rhiancb30-pixel/Esteira-Seletora/Imagens do Projeto/20251215_132234.jpg

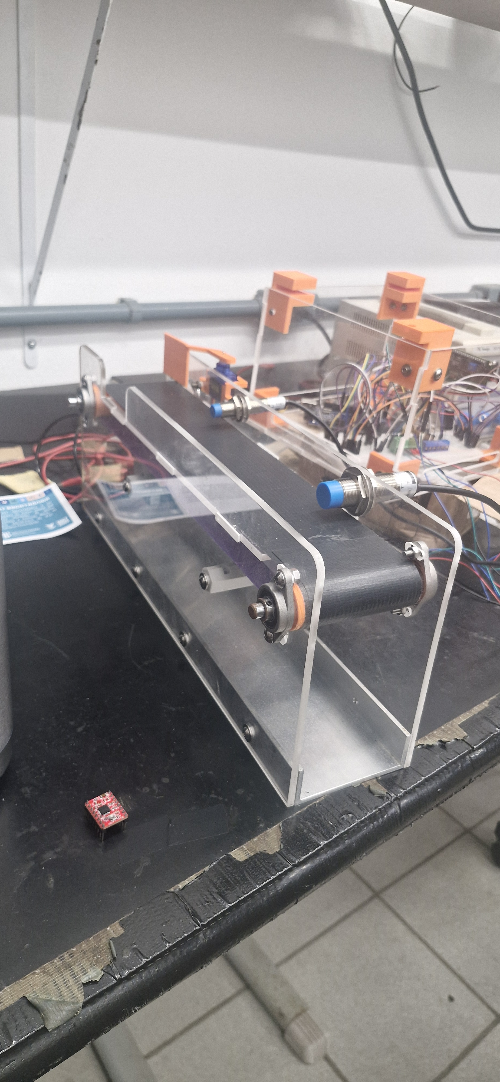
Imagens do Projeto/20251215_132234.jpg
