rhiancb30-pixel/Esteira-Seletora/Imagens do Projeto/20251215_132237.jpg

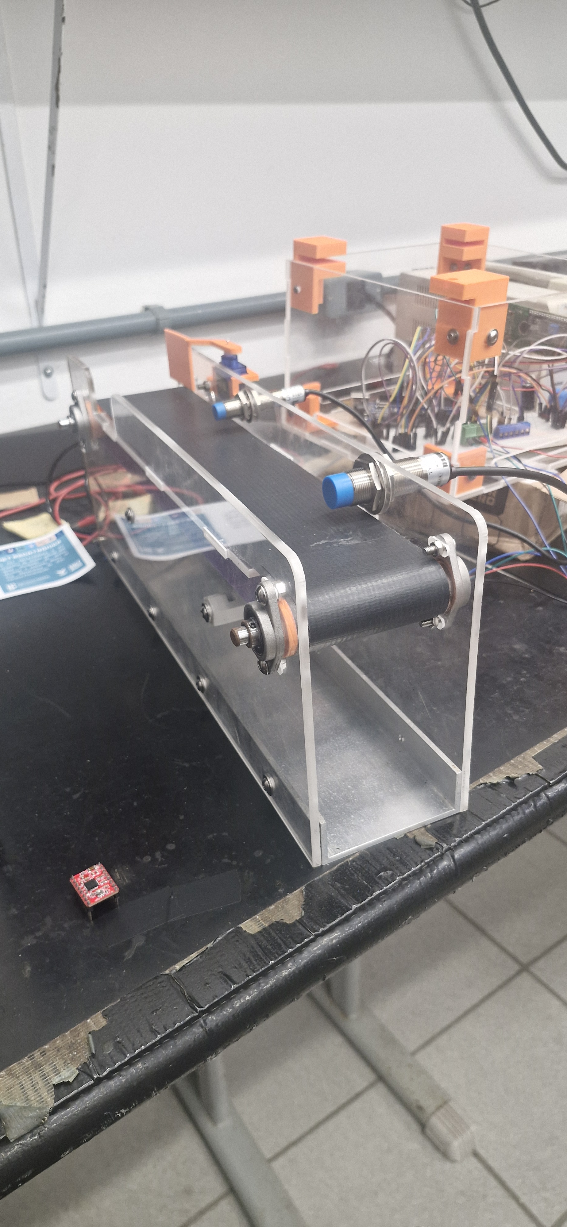
Imagens do Projeto/20251215_132237.jpg
