rhiancb30-pixel/Esteira-Seletora/Caixa/cantoneira_4.SLDPRT

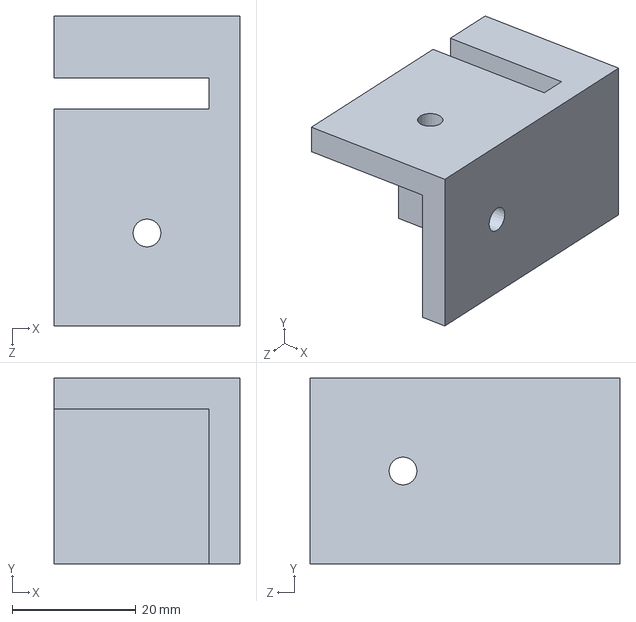
[picture p20: CAD file, 2025-12-16]
Caixa/cantoneira_4.SLDPRT
30.0 x 30.0 x 50.0 mm
