rhiancb30-pixel/Esteira-Seletora/Esteira/Rolete.SLDPRT

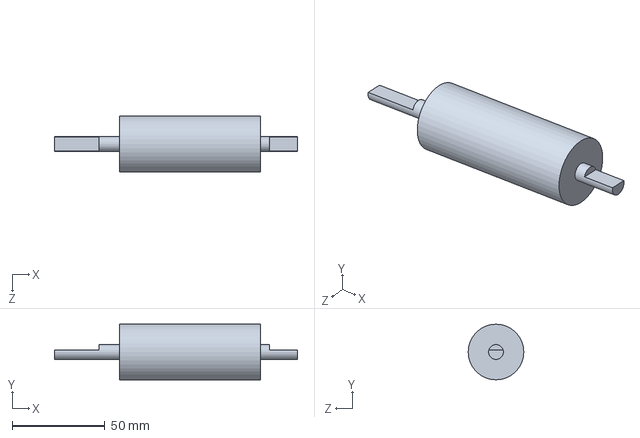
[picture p21: CAD file, 2025-12-16]
Esteira/Rolete.SLDPRT
131.0 x 30.0 x 30.0 mm
