rhiancb30-pixel/Esteira-Seletora/Caixa/Base.SLDPRT

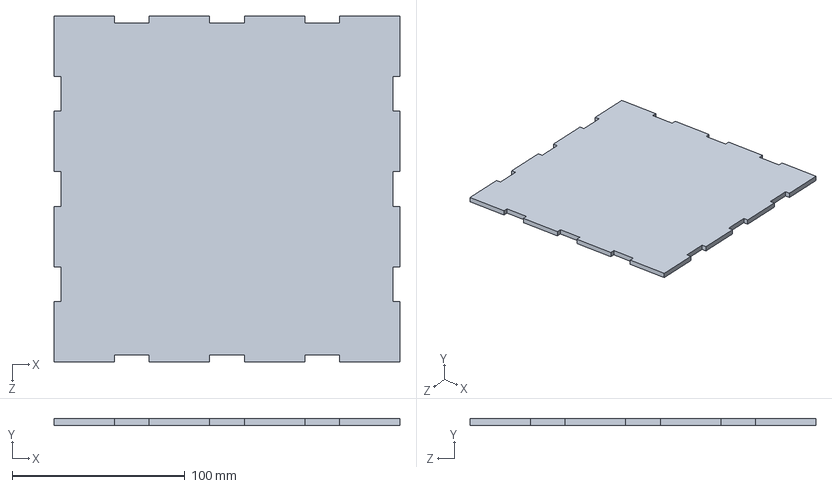
[picture p22: CAD file, 2025-12-16]
Caixa/Base.SLDPRT
200.0 x 4.00 x 200.0 mm
