rhiancb30-pixel/Esteira-Seletora/Esteira/LateralB.SLDPRT

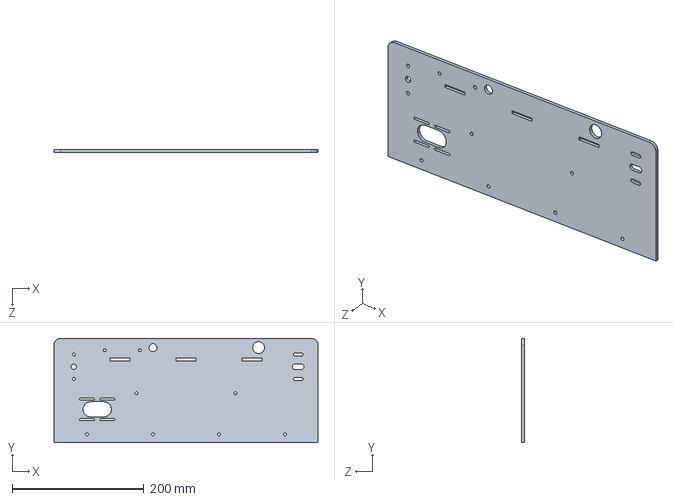
[picture p23: CAD file, 2025-12-16]
Esteira/LateralB.SLDPRT
400.0 x 158.0 x 4.00 mm
