rhiancb30-pixel/Esteira-Seletora/Caixa/TampaCaixa.SLDPRT

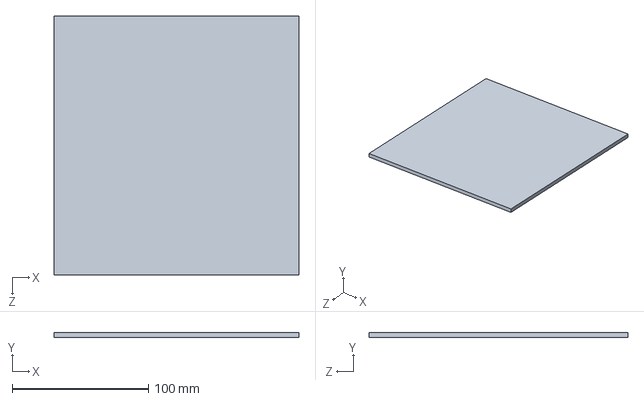
[picture p24: CAD file, 2025-12-16]
Caixa/TampaCaixa.SLDPRT
180.0 x 4.00 x 190.0 mm
