rhiancb30-pixel/Esteira-Seletora/Esteira/PisoFixador.SLDPRT

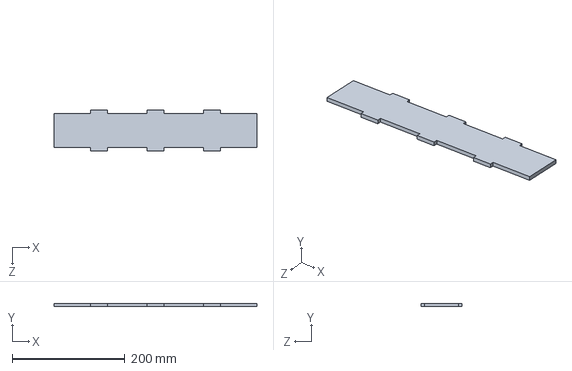
[picture p25: CAD file, 2025-12-16]
Esteira/PisoFixador.SLDPRT
360.0 x 6.00 x 72.0 mm
