rhiancb30-pixel/Esteira-Seletora/Caixa/cantonera.SLDPRT

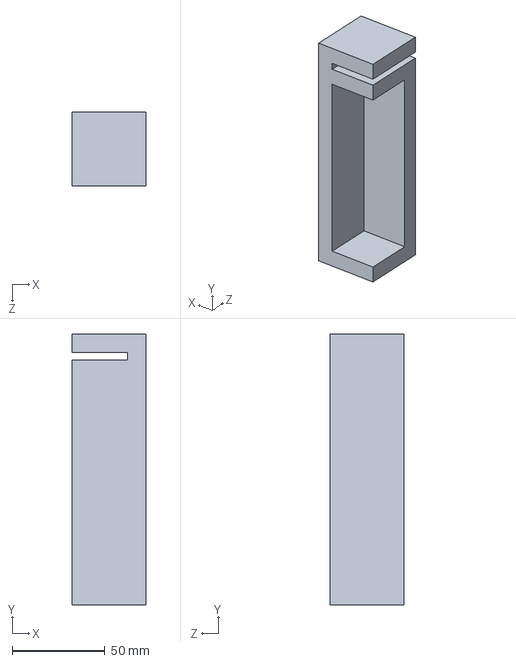
[picture p26: CAD file, 2025-12-16]
Caixa/cantonera.SLDPRT
40.0 x 146.0 x 40.0 mm
