rhiancb30-pixel/Esteira-Seletora/Esteira/Rolete 2.SLDPRT

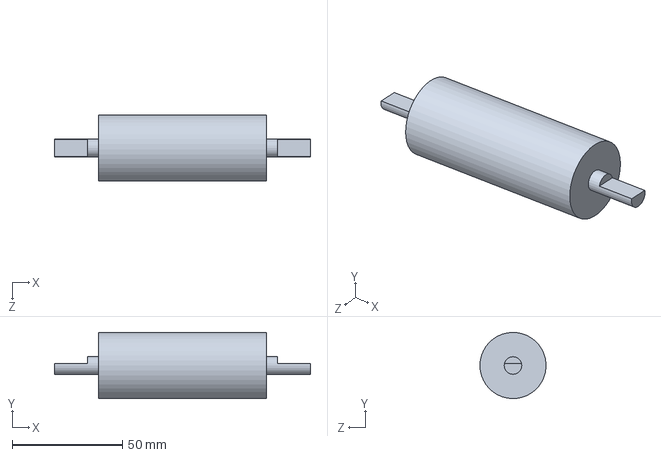
[picture p27: CAD file, 2025-12-16]
Esteira/Rolete 2.SLDPRT
116.0 x 30.0 x 30.0 mm
