rhiancb30-pixel/Esteira-Seletora/Caixa/cantoneira com trava.SLDPRT

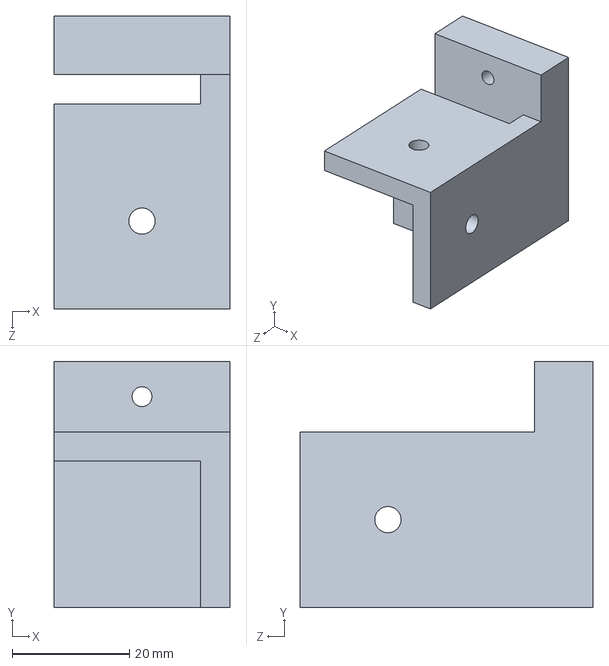
[picture p28: CAD file, 2025-12-16]
Caixa/cantoneira com trava.SLDPRT
30.0 x 42.0 x 50.0 mm
