rhiancb30-pixel/Esteira-Seletora/Esteira/Lona.SLDPRT

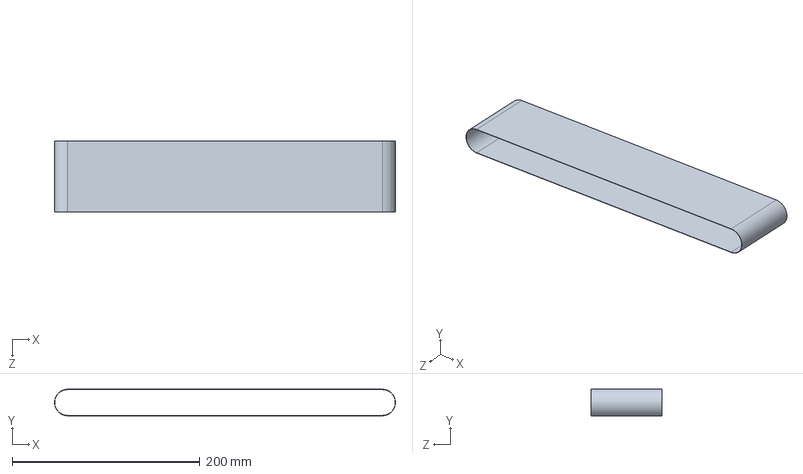
[picture p29: CAD file, 2025-12-16]
Esteira/Lona.SLDPRT
363.2 x 28.3 x 76.0 mm
