rhiancb30-pixel/Esteira-Seletora/Esteira/KFL08 block flange ball bearing 08 diameter shaft.SLDPRT

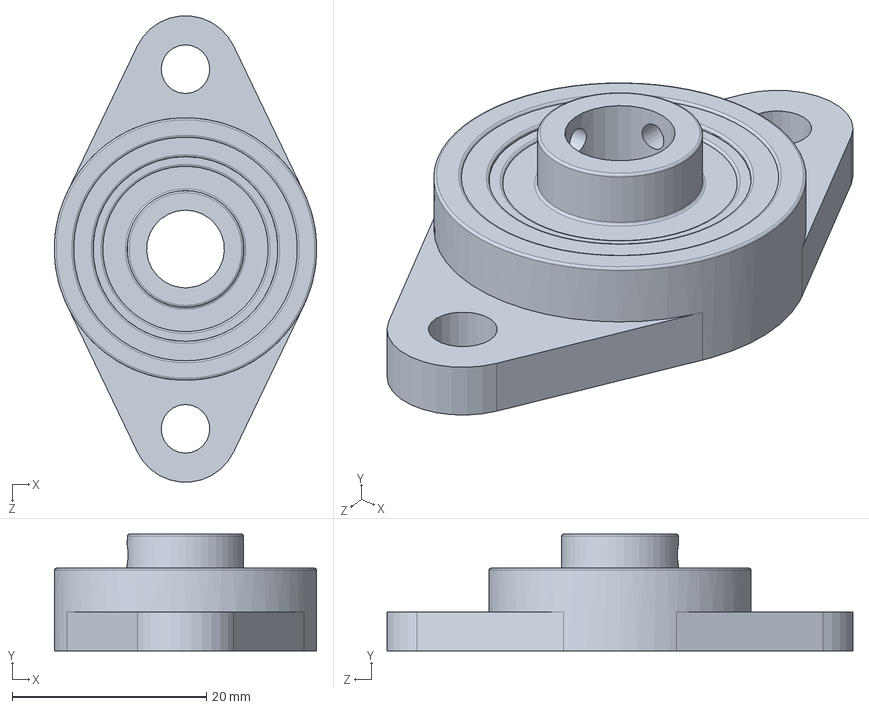
[picture p30: CAD file, 2025-12-16]
Esteira/KFL08 block flange ball bearing 08 diameter shaft.SLDPRT
27.0 x 12.0 x 47.9 mm
