rhiancb30-pixel/Esteira-Seletora/Caixa/lateral LCD.SLDPRT

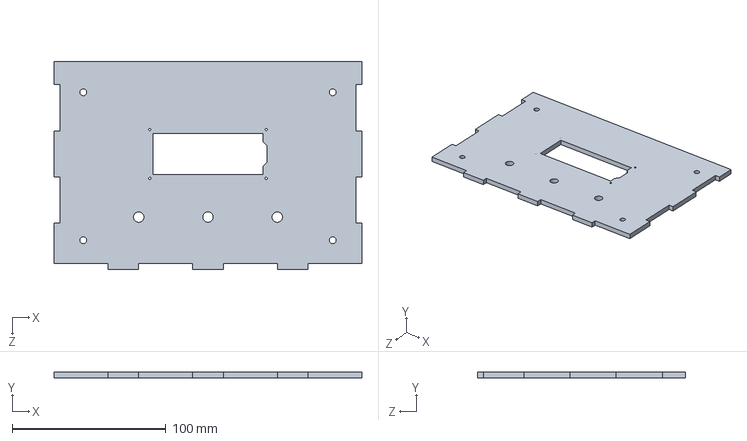
[picture p31: CAD file, 2025-12-16]
Caixa/lateral LCD.SLDPRT
200.0 x 4.00 x 135.0 mm
