rhiancb30-pixel/Esteira-Seletora/Esteira/LCD_I2C_1602.SLDPRT

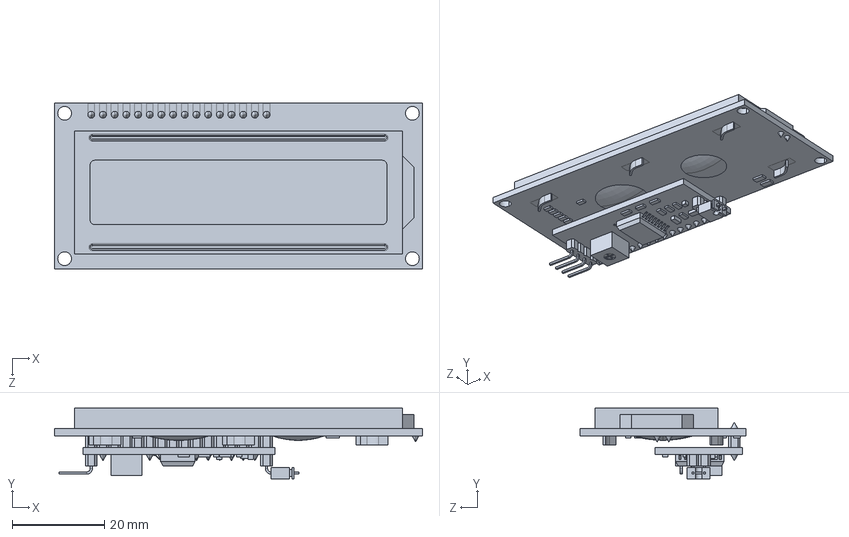
[picture p32: CAD file, 2025-12-16]
Esteira/LCD_I2C_1602.SLDPRT
80.0 x 15.4 x 36.0 mm
