rhiancb30-pixel/Esteira-Seletora/Esteira/GT2_20T.SLDPRT

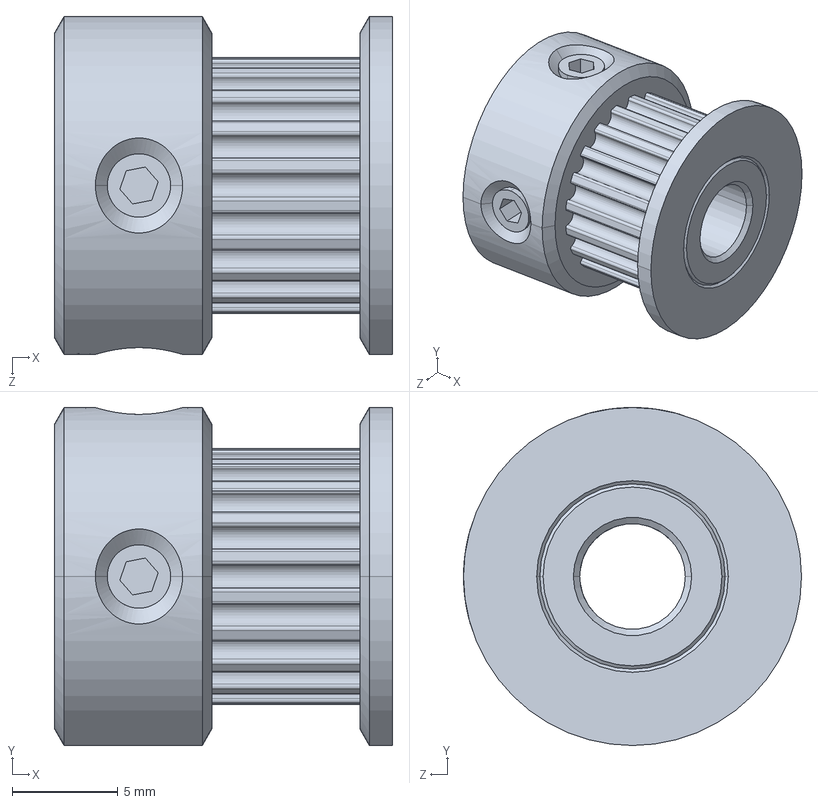
[picture p33: CAD file, 2025-12-16]
Esteira/GT2_20T.SLDPRT
16.0 x 16.0 x 16.0 mm
