rhiancb30-pixel/Esteira-Seletora/Esteira/Perfil metálico frente.SLDPRT

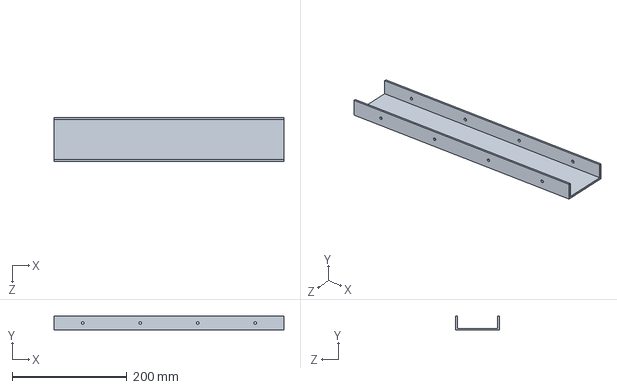
[picture p34: CAD file, 2025-12-16]
Esteira/Perfil metálico frente.SLDPRT
400.0 x 25.0 x 76.0 mm
