rhiancb30-pixel/Esteira-Seletora/Esteira/A4988-Stepper-Driver-Socketed.stp

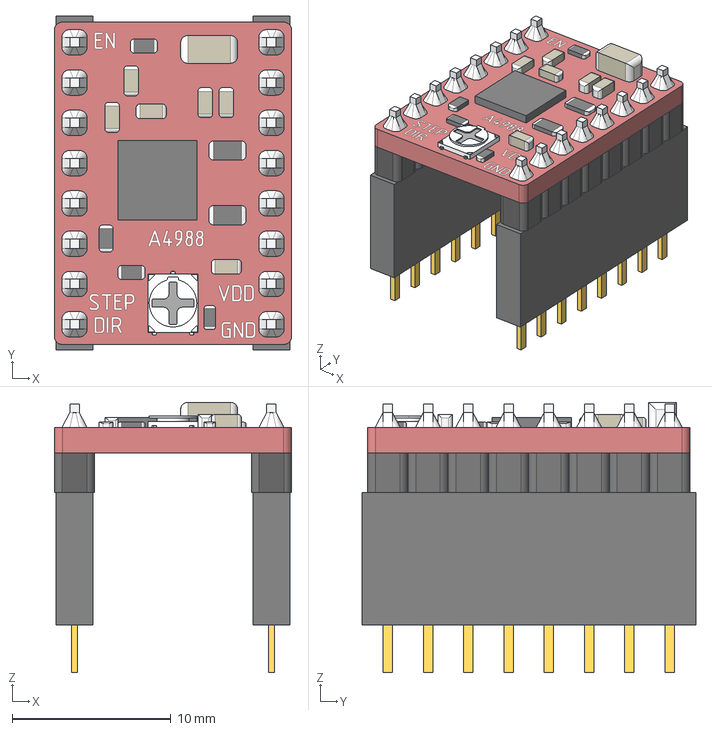
[picture p35: CAD file, 2025-12-16]
Esteira/A4988-Stepper-Driver-Socketed.stp
15.0 x 21.1 x 17.1 mm
