rhiancb30-pixel/Esteira-Seletora/Esteira/[4145] TowerPro SG90 Mini Servo-SunRobotics_in-Pt3.SLDPRT

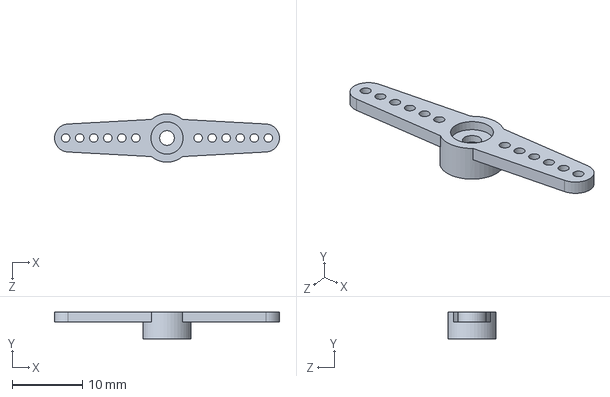
[picture p36: CAD file, 2025-12-16]
Esteira/[4145] TowerPro SG90 Mini Servo-SunRobotics_in-Pt3.SLDPRT
32.1 x 3.80 x 6.90 mm
