rhiancb30-pixel/Esteira-Seletora/Esteira/[4145] TowerPro SG90 Mini Servo-SunRobotics_in-Pt1.SLDPRT

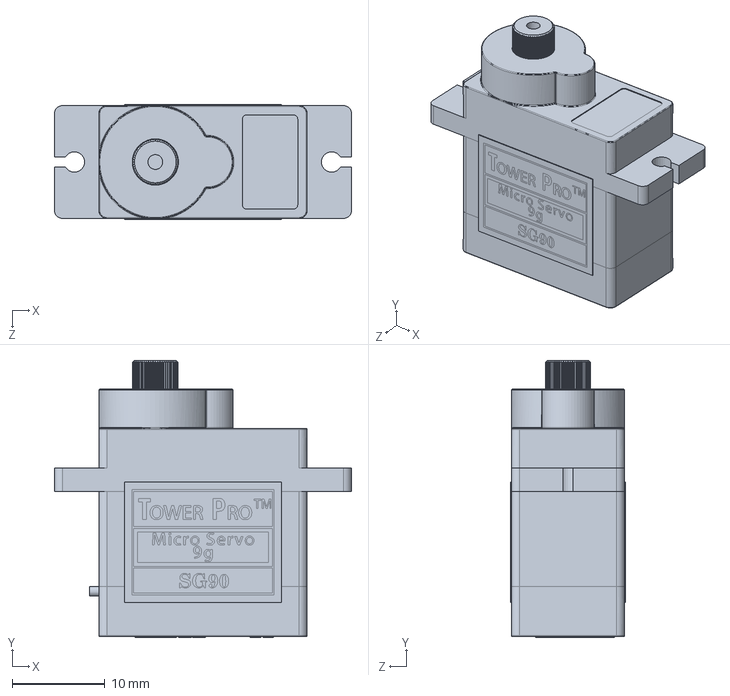
[picture p37: CAD file, 2025-12-16]
Esteira/[4145] TowerPro SG90 Mini Servo-SunRobotics_in-Pt1.SLDPRT
32.1 x 30.0 x 12.4 mm
