rhiancb30-pixel/Esteira-Seletora/Esteira/eixo2.SLDPRT

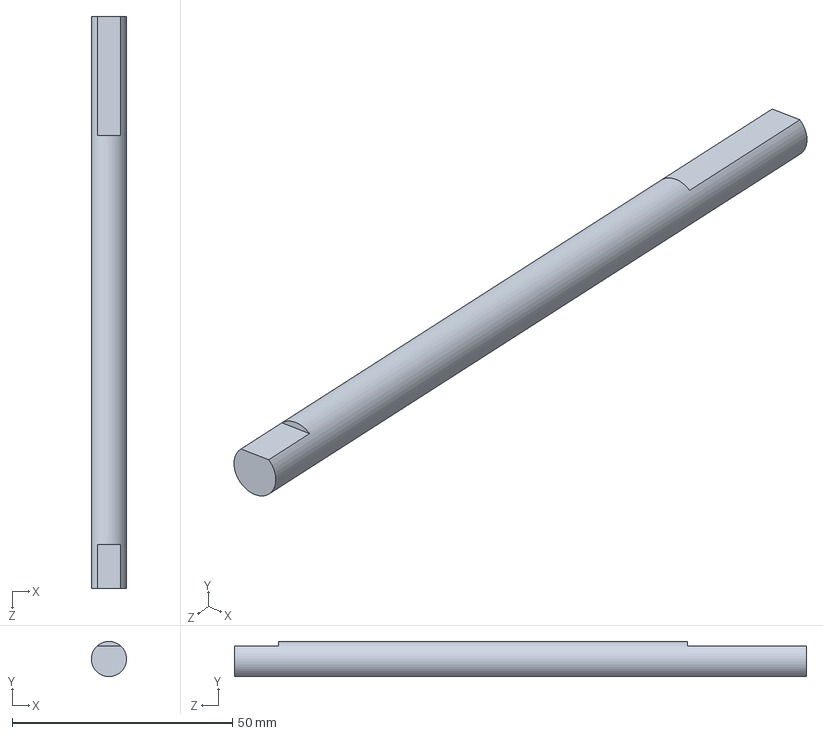
[picture p38: CAD file, 2025-12-16]
Esteira/eixo2.SLDPRT
7.99 x 7.99 x 130.0 mm
