rhiancb30-pixel/Esteira-Seletora/Esteira/Espacador.SLDPRT

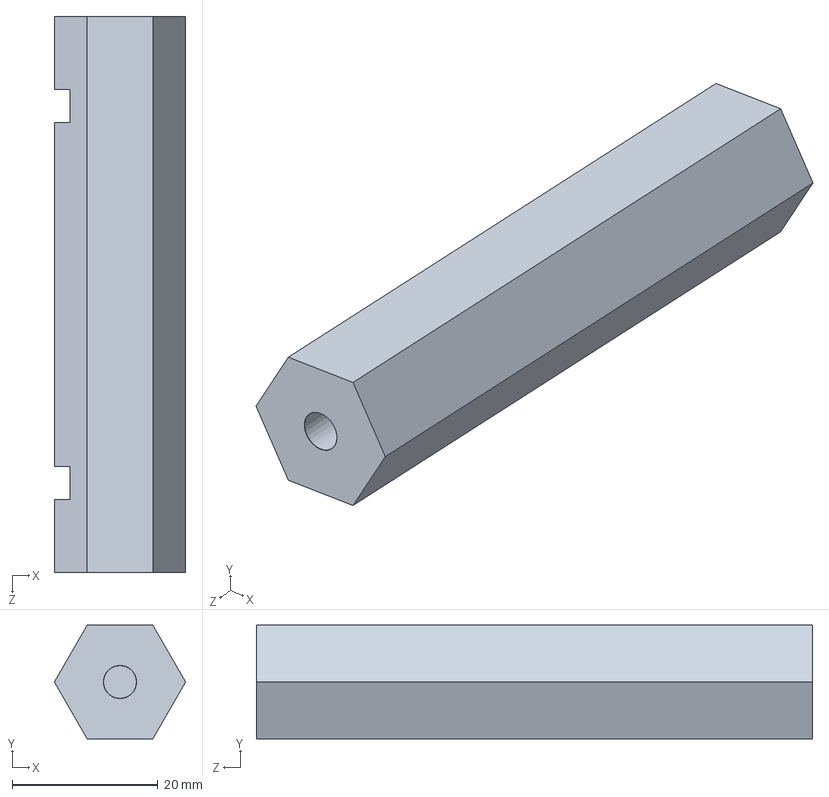
[picture p39: CAD file, 2025-12-16]
Esteira/Espacador.SLDPRT
18.0 x 15.6 x 76.2 mm
