rhiancb30-pixel/Esteira-Seletora/Esteira/eixo1.SLDPRT

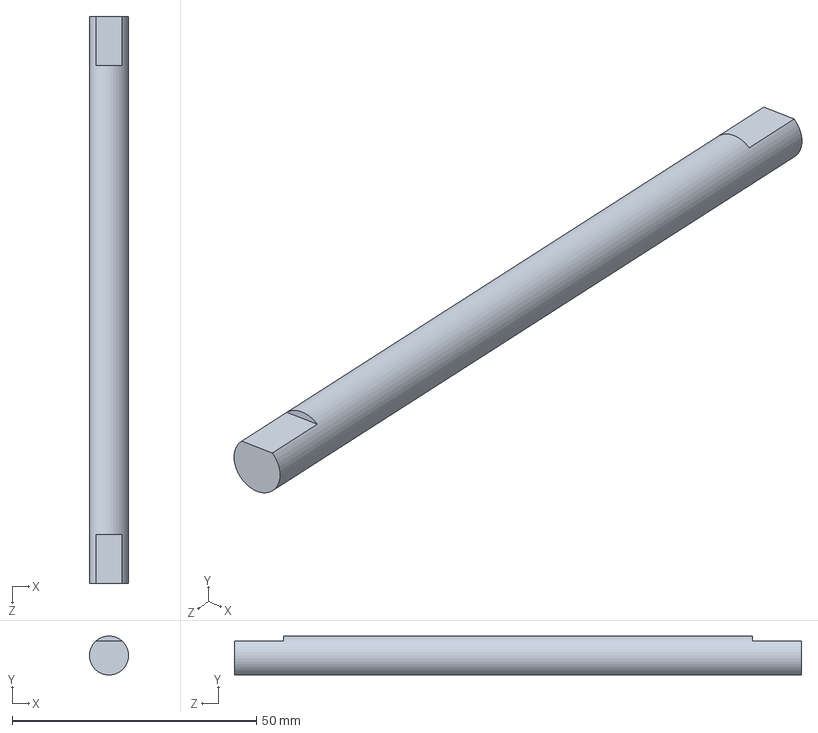
[picture p40: CAD file, 2025-12-16]
Esteira/eixo1.SLDPRT
8.00 x 7.98 x 116.0 mm
